norbertg1/WateringSystem_client-SW/client/certificates.h

#ifndef CERT_H
#define CERT_H

unsigned char certificates_esp8266_bin_crt[] = {
  0x30, 0x82, 0x03, 0x51, 0x30, 0x82, 0x02, 0x39, 0x02, 0x09, 0x00, 0x9f,
  0x90, 0x2e, 0x4f, 0x9c, 0xe1, 0x11, 0xb6, 0x30, 0x0d, 0x06, 0x09, 0x2a,
  0x86, 0x48, 0x86, 0xf7, 0x0d, 0x01, 0x01, 0x0b, 0x05, 0x00, 0x30, 0x7a,
  0x31, 0x0b, 0x30, 0x09, 0x06, 0x03, 0x55, 0x04, 0x06, 0x13, 0x02, 0x48,
  0x55, 0x31, 0x0a, 0x30, 0x08, 0x06, 0x03, 0x55, 0x04, 0x08, 0x0c, 0x01,
  0x61, 0x31, 0x0a, 0x30, 0x08, 0x06, 0x03, 0x55, 0x04, 0x07, 0x0c, 0x01,
  0x61, 0x31, 0x1a, 0x30, 0x18, 0x06, 0x03, 0x55, 0x04, 0x0a, 0x0c, 0x11,
  0x49, 0x72, 0x72, 0x69, 0x67, 0x61, 0x74, 0x69, 0x6f, 0x6e, 0x20, 0x73,
  0x79, 0x73, 0x74, 0x65, 0x6d, 0x31, 0x0c, 0x30, 0x0a, 0x06, 0x03, 0x55,
  0x04, 0x0b, 0x0c, 0x03, 0x63, 0x2e, 0x6f, 0x31, 0x0f, 0x30, 0x0d, 0x06,
  0x03, 0x55, 0x04, 0x03, 0x0c, 0x06, 0x73, 0x65, 0x72, 0x76, 0x65, 0x72,
  0x31, 0x18, 0x30, 0x16, 0x06, 0x09, 0x2a, 0x86, 0x48, 0x86, 0xf7, 0x0d,
  0x01, 0x09, 0x01, 0x16, 0x09, 0x6e, 0x61, 0x40, 0x6e, 0x61, 0x2e, 0x63,
  0x6f, 0x6d, 0x30, 0x1e, 0x17, 0x0d, 0x31, 0x37, 0x30, 0x39, 0x30, 0x35,
  0x31, 0x39, 0x30, 0x34, 0x31, 0x39, 0x5a, 0x17, 0x0d, 0x32, 0x30, 0x30,
  0x39, 0x30, 0x34, 0x31, 0x39, 0x30, 0x34, 0x31, 0x39, 0x5a, 0x30, 0x5b,
  0x31, 0x0b, 0x30, 0x09, 0x06, 0x03, 0x55, 0x04, 0x06, 0x13, 0x02, 0x48,
  0x55, 0x31, 0x0a, 0x30, 0x08, 0x06, 0x03, 0x55, 0x04, 0x08, 0x0c, 0x01,
  0x61, 0x31, 0x0a, 0x30, 0x08, 0x06, 0x03, 0x55, 0x04, 0x07, 0x0c, 0x01,
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
  0x8f, 0xd0, 0x49, 0x08, 0x3c, 0xde, 0x30, 0x9a, 0xe2, 0x11, 0xab, 0xb9,
  0x49, 0x02, 0xe7, 0x2e, 0x58, 0x3d, 0x5b, 0xed, 0xea, 0x23, 0xe9, 0xf5,
  0x03, 0xeb, 0x03, 0x4c, 0xc6, 0x42, 0x27, 0x81, 0x8b, 0x9d, 0xbb, 0x3c,
  0x9b, 0x35, 0xaf, 0xfe, 0x12, 0x3f, 0x39, 0x3c, 0x97, 0x40, 0x9e, 0xe0,
  0xc2, 0xfb, 0x28, 0xec, 0xb4, 0x7e, 0x46, 0x79, 0xca, 0x07, 0x15, 0xb1,
  0xa6, 0x95, 0x8c, 0x15, 0x89, 0x5a, 0x92, 0xf7, 0xda, 0x4d, 0x09, 0x7e,
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
};
unsigned int certificates_esp8266_bin_key_len = 1191;

unsigned int certificates_esp8266_bin_crt_len = 853;

#endif
